pedroctag/Projeto-placa/Software/PBLE02_PROJ.X/config.h

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

#ifndef CONFIG_H
#define CONFIG_H

    #pragma config FOSC = HS                 // Oscilador c/ cristal externo HS
    #pragma config FCMEN = OFF
#pragma config IESO = OFF
#pragma config PWRT = OFF
#pragma config BOR = OFF
#pragma config BORV = 46
    #pragma config WDT=OFF                 // Watchdog controlado por software
    #pragma config WDTPS = 1               // Configura prescaler do watchdog
    #pragma config MCLRE=ON                // Master Clear desabilitado
#pragma config LPT1OSC = OFF
#pragma config PBADEN = ON
#pragma config CCP2MX = ON
#pragma config STVREN = OFF
    #pragma config LVP=OFF                 // Sem programação em baixa tensão
#pragma config XINST = OFF
    #pragma config DEBUG = OFF             // Desabilita debug

#pragma config CP0 = OFF
#pragma config CP1 = OFF
#pragma config CP2 = OFF
#pragma config CP3 = OFF
#pragma config CPB = OFF
#pragma config CPD = OFF

#pragma config WRT0 = OFF
#pragma config WRT1 = OFF
#pragma config WRT2 = OFF
#pragma config WRT3 = OFF
#pragma config WRTB = OFF
#pragma config WRTC = OFF
#pragma config WRTD = OFF

#pragma config EBTR0 = OFF
#pragma config EBTR1 = OFF
#pragma config EBTR2 = OFF
#pragma config EBTR3 = OFF
#pragma config EBTRB = OFF
 
#endif
