pedroctag/Projeto-placa/Software/PBLE02_PROJ.X/io.c

/*
 * File:   io.c
 * Author: Avell
 *
 * Created on 4 de Agosto de 2020, 21:39
 */

#include "bits.h"
#include "io.h"
#include <xc.h>
//PORTB e PORTD apenas para demonstrar o funcionamento


void digitalWrite(int pin, int value){
    //porta
    if(pin <8){
        if (value){  bitSet(PORTA,pin);}
        else{        bitClr(PORTA,pin);}
    }else if(pin<16){
        pin -=8;
        if (value){  bitSet(PORTB,pin);}
        else{        bitClr(PORTB,pin);}
    }else if(pin<24){
        pin -=16;
        if (value){  bitSet(PORTC,pin);}
        else{        bitClr(PORTC,pin);}
    }else if(pin<32){
        pin -=24;
        if (value){  bitSet(PORTD,pin);}
        else{        bitClr(PORTD,pin);}
    }else if(pin<40){
        pin -=32;
        if (value){  bitSet(PORTE,pin);}
        else{        bitClr(PORTE,pin);}
    }
    
	
}
int digitalRead(int pin){
    if(pin <8){
        return bitTst(PORTA,pin);
    }else if(pin<16){
        return bitTst(PORTB,pin-8);
    }else if(pin<24){
        return bitTst(PORTC,pin-16);
    }else if(pin<32){
        return bitTst(PORTD,pin-24);
    }else if(pin<40){
        return bitTst(PORTE,pin-32);
    }
    return -1;
}

void pinMode(int pin, int type) {
    //porta
    if(pin <8){
        if (type){  bitSet(TRISA,pin);}
        else{       bitClr(TRISA,pin);}
    }else if(pin<16){
        if (type){  bitSet(TRISB,pin-8);}
        else{       bitClr(TRISB,pin-8);}
    }else if(pin<24){
        if (type){  bitSet(TRISC,pin-16);}
        else{       bitClr(TRISC,pin-16);}
    }else if(pin<32){
        if (type){  bitSet(TRISD,pin-24);}
        else{       bitClr(TRISD,pin-24);}
    }else if(pin<40){
        if (type){  bitSet(TRISE,pin-32);}
        else{       bitClr(TRISE,pin-32);}
    }
            
}
