pedroctag/Projeto-placa/Software/PBLE02_PROJ.X/led.h

/* 
 * File:   led.h
 * Author: lucas
 *
 * Created on 4 de Julho de 2023, 15:46
 */

#ifndef LED_H
#define	LED_H

void ledInit();
void ledOn(int pos);
void ledOff(int pos);
void ledBlink(int pos);

#endif	/* LED_H */
