pedroctag/Projeto-placa/Software/PBLE02_PROJ.X/output.h

/* 
 * File:   output.h
 * Author: lucas
 *
 * Created on 5 de Junho de 2023, 20:55
 */

#ifndef OUTPUT_H
#define	OUTPUT_H
void outputInit(void);
void outputPrint(int numTela, int idioma);

#endif	/* OUTPUT_H */
